retrobuiltRyan/pixelvision_av1000_mkII/STEP files/PixelVision AV-1000MkII v1.0 - Rear Body.step

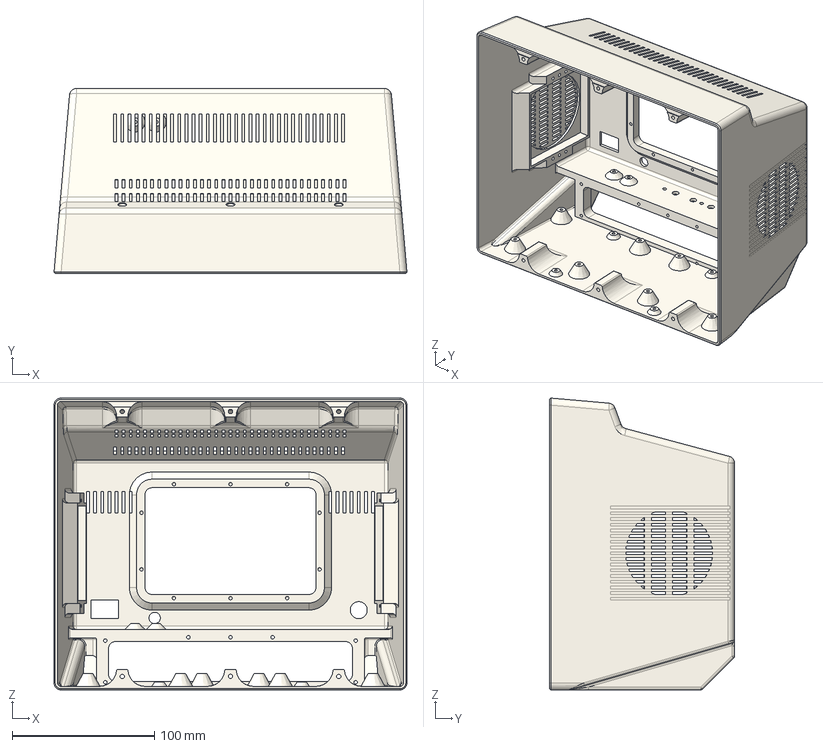
[picture p15: CAD file, 2026-07-17]
STEP files/PixelVision AV-1000MkII v1.0 - Rear Body.step
247.8 x 130.0 x 204.9 mm
