retrobuiltRyan/pixelvision_av1000_mkII/STEP files/PixelVision AV-1000MkII v1.0 Swivel Base - Spring Nut.step

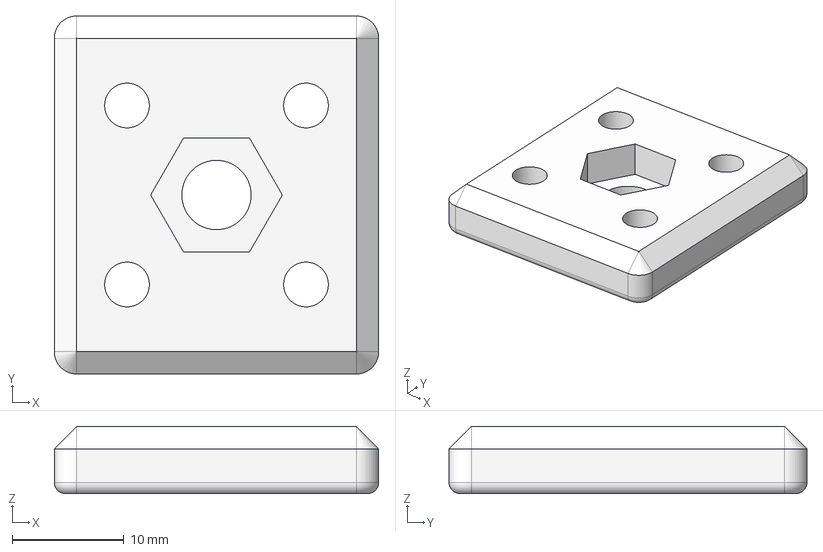
[picture p16: CAD file, 2026-07-17]
STEP files/PixelVision AV-1000MkII v1.0 Swivel Base - Spring Nut.step
29.0 x 32.0 x 6.00 mm
