retrobuiltRyan/pixelvision_av1000_mkII/STEP files/PixelVision AV-1000MkII v1.0 Swivel Base - Curve Washer.step

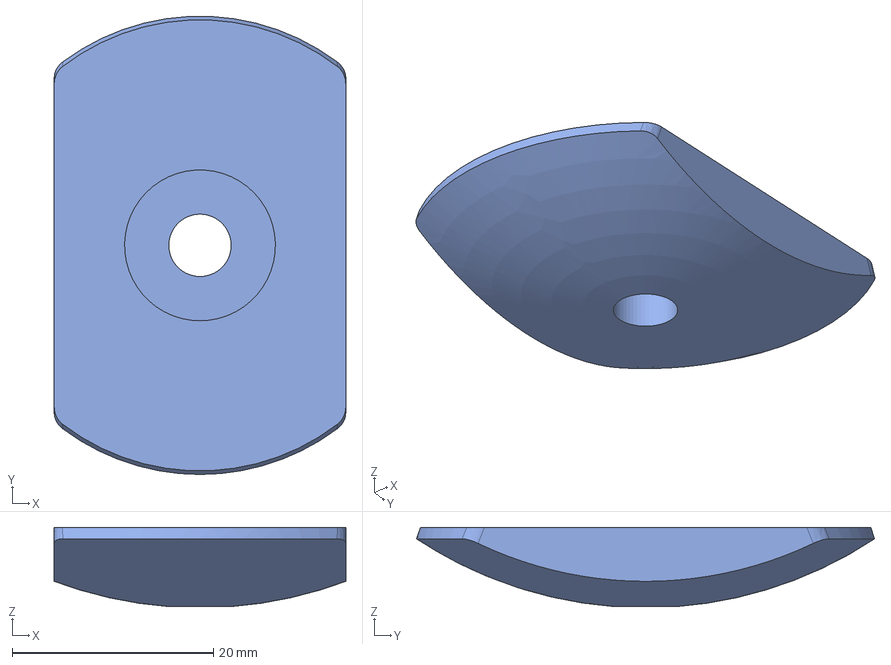
[picture p17: CAD file, 2026-07-17]
STEP files/PixelVision AV-1000MkII v1.0 Swivel Base - Curve Washer.step
29.0 x 45.5 x 7.88 mm
